zwizwa/simtrace/hardware/kicad/SIMtrace.sch

## KiCad design hardware/kicad/SIMtrace.sch (2011-08-13)

Schematic: SIMtrace.sch

Parts:
BT1: 4.5-6V; PIN_ARRAY_2X1
C1, C12: 2.2uF; SM0603
C3, C4, C7, C9, C15, C16, C19, C20, C23, C24: 100nF; SM0603
C5: 33pF; SM0603
C6: 10nF; SM0603
C10: 1nF; SM0603
C11, C13: 15pF; SM0603
C14, C21, C22: 1uF; SM0603
C17, C18: 10pF; SM0603
D1: Schottky; SOD123
D2, D3: 1N5819; SOD123
D4: RED; LED-0805
D5: GREEN; LED-0805
FB1, FB2: FILTER; SM0805
IC2: AP7332; SOT26
IC3: AT91SAM7S; TQFP_64
IC4: CB3Q3244; SSOP20_BDQ
IC5: FPF2005; SOT353
J1: USB; USB-MINI-B_54819-0519
J2: SERIAL; JACK2.5_SJ1-2503A
JP1: TEST; PIN_ARRAY_2X1
JP2: ERASE; PIN_ARRAY_2X1
P1: JTAG; pin_array_10x2
P2: DEBUG; PIN_ARRAY-6X1
P3: FFC_SIM; FFC_REBELSIM
P4: SIM; SIM_AMPHENOL
P5: SAM; SAM_FCI
Q1, Q2: BC847; SOT23_BC847
R1, R4, R5, R6, R7, R8, R12, R19, R22: 100K; SM0603
R2, R16, R17, R18: 10K; SM0603
R3, R11: 1K5; SM0603
R9, R10: 27R; SM0603
R13, R14: 150R; SM0603
R20, R21: 10k1%; SM0603
SW1: RESET; PUSH_BUTTON
SW2: BOOTLOADER; PUSH_BUTTON
U1: FLASH; SOIC8
X1: 18.432MHz; Q_49U3HMS

Notes on the sheet:
MEMORY
LED
DEBUG
PHONE
SIM/SAM SLOTS
POWER
XTAL
PLL
USB
RESET/BOOTLOADER
JTAG
