zwizwa/simtrace/hardware/kicad/microsimffc.sch

## KiCad design hardware/kicad/microsimffc.sch (2011-07-07)

Schematic: microsimffc.sch

Parts:
FFC1, FFC2, FFC3, FFC4: FFC
SIM1, SIM2, SIM3, SIM4: ISO7816_CARD
