zwizwa/simtrace/hardware/kicad/simadapter1.sch

## KiCad design hardware/kicad/simadapter1.sch (2012-02-18)

Schematic: simadapter1.sch

Parts:
P1: REBELSIM
P2: ISO7816_NO
