zwizwa/simtrace/hardware/kicad/simcable.sch

## KiCad design hardware/kicad/simcable.sch (2011-07-02)

Schematic: simcable.sch

Parts:
P_DOWN2: FFC
P_LEFT3: FFC
P_RIGHT4: FFC
P_UP1: FFC
SIM_DOWN2: ISO7816_CARD
SIM_LEFT3: ISO7816_CARD
SIM_RIGHT4: ISO7816_CARD
SIM_UP1: ISO7816_CARD
